CGShepherd/Shellac/docs/design_pack/AE-075G_SCH108_Output_Interface_and_PRE90_Compatibility_Reconciliation_Rev_A0.md

# AE-075G — SCH108 Output Interface and PRE90 Compatibility Reconciliation — Rev A0

**Project:** Shellac
**Status:** CLOSED — OUTPUT INTERFACE ELECTRICAL/NATIVE MIGRATION VALIDATED; MANUAL XY PLACEMENT OPEN
**Baseline:** `2d635647cd3ee6e4e1886cbfcbfffe43f3453116` (AE-075F)

## Purpose

AE-075G closes the SCH108 PCB-to-rear-panel balanced-output connector electrical/native migration, corrects the live THAT1646 output-source-impedance semantics, and executes an application-specific Topping PRE90 2 kOhm load discriminator without modifying historical AE-069 RUN06 evidence.

## Output harness

Selected hardware: Molex `5055780221` two-circuit right-angle SMT PCB header, `5055700201` housing and `5055721200` female crimp. H801 is left and H802 right. Pin 1 is HOT/+, pin 2 COLD/-, retention pads are mechanical/unconnected, and no 0VA conductor is present. Rear-panel XLR pin 1 and shell remain local CHASSIS bonds under AE-075B.

Native F8 validation proves H801 pad 1 `/OUTPUT_L_POS`, pad 2 `/OUTPUT_L_NEG`; H802 pad 1 `/OUTPUT_R_POS`, pad 2 `/OUTPUT_R_NEG`; retention pads are unconnected.

The imported/autogenerated H801/H802 XY coordinates are explicitly not routing or placement authority. Manual front-to-rear placement reconciliation remains open.

## THAT1646 source semantics

The live generator model records 25 Ohm output impedance per leg and 50 Ohm differential/balanced. This resolves `AE071-S01`.

## PRE90 application-specific load discriminator

The PRE90 2 kOhm balanced-input case is separate from the AE-069 RUN06 normal-load set.

- Worst absolute insertion loss versus 100 kOhm: **0.209239 dB**.
- Worst passband peak: **0.000409 dB**.
- DC absolute gate: **PASS**.
- Exact-topology HF small-signal evidence: **COMPLETE**.
- 3.21 Vrms local severe-input headroom minimum: **PASS**.
- Overall 2 kOhm load compatibility: **PASS**.

Loaded representative Shellac estimates are 0.626735 Vrms nominal, 5.720666 Vrms worst-default and 9.098397 Vrms worst-high-gain. Margins to the controlled 9.3 Vrms PRE90 0 dB balanced-input sensitivity figure are respectively 23.4280 dB, 4.2207 dB and 0.1904 dB.

The 2 kOhm electrical load is therefore accepted, but the highest representative high-gain state retains a commissioning/operating-level check because only about 0.19 dB margin exists to the published sensitivity figure.

## Configuration-control debt reconciliation

AE-075G closure also reconciles temporal coupling in recent historical assurance tests. Historical AE tests now assert the design facts and qualification boundaries owned by their own records rather than requiring later live routing-hold status, global product-population counts or unrelated blocker sets to remain frozen. Mutable current authority remains owned by `tests/test_current_decision_index.py`. A dedicated regression guard prevents the identified anti-patterns from being reintroduced across AE-071 through AE-075G assurance tests.

## Preserved boundaries

AE-075G does not modify historical AE-069 RUN06 evidence or normal-load definitions; close RUN06 prototype load/cable stability; close dynamic THD; select the final ferrite; authorise routing/layout/BOM/manufacturing freeze; freeze H801/H802 XY/orientation; or change the AE-075F B03 four-local-control-module authority.

The next controlled mechanical increment will address six-point direct main-PCB-to-top-cover support and deliberate manual front-to-rear placement. It must explicitly supersede the AE-075F carrier/local-control-board assumptions rather than rewrite AE-075D/E/F history.

## Evidence

- `simulation/config/ae075g_pre90_output.yaml`
- `simulation/scripts/ae075g_pre90_output.py`
- `simulation/results/ae075g_pre90_output/ae075g_pre90_output.json`
- `simulation/results/ae075g_pre90_output/ae075g_pre90_output.md`
- `tests/test_ae075g_output_interface_phase1.py`
- `tests/test_ae075g_output_interface_phase2.py`

This record is retained only if the fail-closed Phase-2B closure script completes targeted/full regression, deterministic generated-CAD rebuild, native hierarchical ERC, native PCB integrity, integrated preflight, decision/configuration audit and `git diff --check`.
