CGShepherd/Shellac/docs/design_pack/AE-040A_Post_F03_Production_Integrity_Reconciliation_Rev_A0.md

# AE-040A — Post-F03 Production Integrity Reconciliation

**Revision:** A0  
**Status:** ROUTING-HOLD RECONCILIATION

AE-036 originally imposed a repository-wide routing hold on:
- F01 — native PCB deletion risk;
- F02 — SCH101 cartridge load/bias/RF incompleteness;
- F03 — dual op-amp package/unit semantics.

All three are now closed by controlled, regression-tested increments.

## Closure evidence

### F01
AE-036A/B preserve native PCB and design-rule artifacts during normal clean builds.

### F02
AE-037 family closes the balanced cartridge interface and reconciles placement.

### F03
AE-038/039 family closes the 18-function / 10-package op-amp representation,
real KiCad A/B units, actual SOIC-8 pins, and explicit follower feedback.

## Disposition

The **AE-036 repository-wide routing hold is lifted**.

F04-F13 remain open. This does not constitute fabrication release. Analogue
routing may resume under SR-041 authority while controls, supply margin, BOM,
native-audit strength, CI, mechanical interface confirmation and release evidence
continue toward closure.
