CGShepherd/Shellac/docs/design_pack/AE-030_Generated_Production_Readiness_Audit.md

# AE-030 Generated Production Readiness Audit

Repository: `C:\Users\chris\Dropbox\000_Projects\000_Audio\Shellac`

## Executive status

- production gates: **18**
- CLOSED: **4**
- READY_FOR_NEXT_ACTIVITY: **6**
- PROTOTYPE_EVIDENCE_REQUIRED: **1**
- BLOCKED: **7**
- release blockers: **10**

## Gate matrix

| ID | Area | State | Release blocker | Evidence | Next action |
|---|---|---|---|---|---|
| ELEC-SIGNAL | Electrical signal chain | **CLOSED** | NO | AE-023 + AE-029; DR-037/038/039/040 implemented; analytical acceptance matrix established. | Do not reopen unless prototype evidence contradicts the controlled model. |
| ELEC-MEASURE | Prototype electrical acceptance | **PROTOTYPE_EVIDENCE_REQUIRED** | YES | AE-029 defines measured CMRR/noise/DC/EQ/overload/transient acceptance. | Build representative hardware and execute commissioning matrix. |
| MECH-ENCLOSURE | Audio enclosure / carrier / PCB datum | **CLOSED** | NO | SR-040 freezes METCASE M5502119 evidence and 220 x 140 mm PCB datum. | Retain frozen datum unless a production ECO is justified. |
| MECH-CONTROLS | Rotary control mechanics | **BLOCKED** | YES | Grayhill 71BDF30 is rejected for right-angle geometry; AE-026/027/028 select Lorlin PT pending exact MPN/sample evidence. | Close Lorlin exact-order-code and physical sample geometry gates, then perform control-hardware ECO. |
| MECH-TOP | Top-panel machining | **BLOCKED** | YES | Current top-cover stack still encodes Grayhill geometry and explicitly withholds machining release. | Regenerate top-cover stack from verified Lorlin PT + C&K hardware and panel thickness. |
| PCB-OUTLINE | PCB outline and mounting | **CLOSED** | NO | SR-040 frozen outline / four mounting holes / keep-outs. | Carry frozen outline into native board. |
| PCB-PLACEMENT | Critical placement | **READY_FOR_NEXT_ACTIVITY** | NO | SR-041 accepts manual clusters as routing baseline with zero mounting collisions. | Only local refinement within movement authority during routing. |
| PCB-NATIVE | Native KiCad board setup | **READY_FOR_NEXT_ACTIVITY** | YES | SR-043 audit requires populated frozen outline, mounting holes, unrouted state and four copper layers. | Confirm native board is four-layer: F.Cu/In1.Cu/In2.Cu/B.Cu before routing. |
| PCB-ROUTING | Native PCB routing | **BLOCKED** | YES | Current native-board audit intentionally expects an unrouted board before routing release. | Complete controlled manual routing, planes, return paths, then DRC/ERC/review. |
| PCB-FAB | Fabrication release | **BLOCKED** | YES | No production-routed/DRC-closed fabrication baseline exists yet. | After routing: run DRC/ERC, Gerber/drill inspection, fabrication manifest and release review. |
| BOM-CONTROLS | Control-hardware BOM | **BLOCKED** | YES | Controlled BOM still contains rejected Grayhill rotary parts. | Replace only after Lorlin PT production MPN/sample gate closes. |
| BOM-GENERAL | General BOM/procurement | **READY_FOR_NEXT_ACTIVITY** | YES | Controlled partial BOM exists; procurement_complete is false. | Run final BOM completeness, alternates, lifecycle and availability audit before production release. |
| DOC-AUTHORITY | Decision/document authority | **CLOSED** | NO | AE-024/025 reconciliation: zero vocabulary findings and zero current-authority contradictions. | Maintain authority classifications with future ECOs. |
| DOC-COMMISSION | Commissioning / maintenance baseline | **READY_FOR_NEXT_ACTIVITY** | NO | AE-029 provides first-hardware acceptance matrix; maintenance structure exists. | Populate measured results and fault-isolation guidance after prototype. |
| DOC-RELEASE | Production design pack | **BLOCKED** | YES | Pack structure exists but fabrication release, measured acceptance, final BOM and release manifest remain incomplete. | Assemble release pack after PCB/mechanical/prototype gates close. |
| REPRO-CLEANCLONE | Clean-clone reproducibility | **BLOCKED** | YES | Not yet demonstrated from an empty clone against pinned tool/dependency versions. | Perform clean-clone build and compare generated production artifacts before tag. |
| REPO-HYGIENE | Repository production cleanup | **READY_FOR_NEXT_ACTIVITY** | NO | Cleanup deliberately deferred until production standard is known. | Classify authoritative source, controlled evidence and release artifacts; archive/remove detritus after baseline freeze. |
| INFRA-EXTRACT | Foundry / Generator extraction | **READY_FOR_NEXT_ACTIVITY** | NO | Planned post-production extraction; Shellac still informs generic/project-specific boundary. | Extract Foundry and Generator only after production clean-clone baseline is proven. |

## Required design-pack path check

- All AE-030 required authority/acceptance paths are present.

## Live Grayhill references requiring ECO disposition

- `config/bom/shellac_bom.yaml`
- `config/procurement/sourcing_snapshot_2026-08-24.yaml`
- `generator/mechanical/control_hardware.py`
- `generator/mechanical/top_cover_stack.py`
- `generator/model/controls.py`
- `generator/model/production_readiness.py`

## Recommended execution order

1. Close Lorlin PT exact MPN and AE-028 mechanical sample gate.
2. Perform control-hardware ECO: BOM + mechanical model + top-cover stack + footprints/placement.
3. Confirm native KiCad board four-layer stack and plane intent.
4. Route the native PCB under SR-041 critical-net/manual-routing rules.
5. Run full DRC/ERC, return-path/plane review and fabrication-output inspection.
6. Complete general BOM/procurement/lifecycle audit.
7. Fabricate and commission representative hardware using AE-029.
8. Freeze measured acceptance limits and complete maintenance/fault-isolation data.
9. Assemble production design/release pack.
10. Clean-clone reproducibility audit.
11. Repository cleanup and tagged production release.
12. Extract Foundry and Generator into independent versioned dependencies.

## Interpretation

The project is no longer primarily blocked by signal-chain design.
The critical path is now controls/mechanics -> native routing/fabrication -> prototype evidence -> release/reproducibility.
