CGShepherd/Shellac/docs/procurement/AE028_PT_Mechanical_Sample_Basket.md

# AE-028 PT mechanical sample basket

Preferred sources: established UK distributors.

Indicative basket:
- 1 × Lorlin PT6534 or equivalent PT 2P5T mechanical proxy
- 1 × Lorlin PT6528 spacer kit
- 1 × Lorlin PT602-003 or PT602-011 additional wafer

Important:
These are for mechanical validation only. Do not substitute them into the
production BOM for the required gold-contact switches.
