CGShepherd/Shellac/docs/design_pack/AE-025_Current_Authority_and_Design_Pack_Reconciliation_Rev_A0.md

# AE-025 — Current Authority and Design-Pack Reconciliation

**Revision:** A0
**Base:** `develop` at `47a5fcabfef4239fcfe78bf97901dce75b4e7301`

AE-024 reported 26 apparent status contradictions. Most are valid historical-state
evidence rather than current defects. AE-025 therefore reconciles only present-tense
authority surfaces.

Changes:
- separates narrative lifecycle statuses from authoritative current statuses;
- adds explicit current-authority vs historical-evidence classification;
- updates README from stale SR-034/G3-023 baseline language;
- updates design-pack index for implemented DR-038/039 and AE-023;
- updates maintenance skeleton for implemented service links/DC block;
- teaches AE-024 to report contradictions only on current-authority surfaces.

Historical AE-016/017/019/020 records remain unchanged.

Expected result after rerunning AE-024:
- zero status-vocabulary findings;
- zero unexpected current-authority contradictions;
- numerous baseline keyword hits may remain because historical analyses correctly
  record the baseline they examined.
