CGShepherd/Shellac/docs/AE-022_DR038_Full_SCH101_Precision_Migration_Rev_A0.md

# AE-022 — DR-038 Full SCH101 Precision Migration

Large subsystem migration: 4x LT5400-7 differential converter, low-impedance
precision gain legs, service-link configuration, native KiCad symbol/footprint,
placement ownership, BOM and decision-register migration. Once this reaches
green pytest plus normal build/ERC, proceed to full schematic human review/ERC
and then PCB layout.
