CGShepherd/Shellac/docs/AE-022F_LT5400_Symbol_Contract_Closure_Rev_A0.md

# AE-022F — LT5400 Symbol-Contract Closure

AE-022E showed that the remaining defect lies at the LT5400 primitive boundary.

AE-022F gives the LT5400 a deliberately spacious logical schematic symbol while
preserving the physical MS8E footprint and pin numbering. Pins 1–4 are separated
on the left, pins 5–8 on the right, and EP9 is isolated below the body.

SCH101 returns to explicit conductive geometry because the internal electrical
audit does not electrically join identical labels at separate coordinates.

Primitive-level tests now verify nine unique semantic pin locations before the
SCH101 builder is exercised.
