CGShepherd/Shellac/docs/AE-017_Generated_Atomic_Migration_Dependency_Map.md

# AE-017 Generated DR-038 / DR-039 Dependency Map

Repository scanned: `C:\Users\chris\Dropbox\000_Projects\000_Audio\Shellac`

## Summary

- matched files: **80**
- matched references: **505**

This report is evidence for an atomic migration. A file appearing here is
not automatically changed; it is a review surface that must be dispositioned.

## SCH101_NUMERIC

| File | Contract class | References |
|---|---|---:|
| `docs/AE-010_SCH101_Gain_Selector_Closure_Rev_A.md` | controlled documentation | 2 |
| `docs/AE-011_End_to_End_Signal_Chain_Closure_Rev_A0.md` | controlled documentation | 1 |
| `docs/AE-013_SCH101_Noise_CMRR_Review_Rev_A0.md` | controlled documentation | 1 |
| `docs/AE-014_SCH101_Precision_Architecture_Downselect_Rev_A0.md` | controlled documentation | 7 |
| `docs/AE-016A_AE016_Regression_Repair_Rev_A0.md` | controlled documentation | 1 |
| `docs/AE-017_Atomic_Migration_Dependency_Mapping_Gate_Rev_A0.md` | controlled documentation | 4 |
| `docs/decisions/DR-038_SCH101_Precision_Architecture_SELECTED.md` | controlled documentation | 1 |
| `generator/blocks/balanced_input.py` | CAD builder | 12 |
| `generator/core/components.py` | CAD infrastructure | 1 |
| `generator/model/balanced_input.py` | electrical/analysis model | 13 |
| `generator/model/sch101_precision_analysis.py` | electrical/analysis model | 4 |
| `generator/model/sch101_precision_candidate.py` | electrical/analysis model | 1 |
| `out/kicad/ProjectShellac_SCH101.kicad_sch` | repository/support | 18 |
| `out/kicad/ProjectShellac_SCH103.kicad_sch` | repository/support | 1 |
| `out/layout/footprint_contract.json` | repository/support | 14 |
| `out/layout/kicad_native_pipeline.json` | repository/support | 14 |
| `out/pcb/ProjectShellac_Gate3A_Review.kicad_pcb` | repository/support | 14 |
| `scripts/report_balanced_input_gain.py` | repository/support | 4 |
| `tests/test_ae017_dependency_map.py` | regression contract | 5 |
| `tests/test_balanced_input.py` | regression contract | 5 |
| `tests/test_balanced_input_gain.py` | regression contract | 3 |
| `tests/test_dr038_dr039.py` | regression contract | 3 |
| `tools/ae017_dependency_map.py` | repository/support | 12 |

## SCH101_CAD

| File | Contract class | References |
|---|---|---:|
| `docs/AE-017_Atomic_Migration_Dependency_Mapping_Gate_Rev_A0.md` | controlled documentation | 4 |
| `docs/SR-006_SCH101_DIP_Switch_Closure_Rev_A.md` | controlled documentation | 1 |
| `generator/blocks/balanced_input.py` | CAD builder | 5 |
| `generator/core/components.py` | CAD infrastructure | 1 |
| `generator/core/pins.py` | CAD infrastructure | 1 |
| `generator/layout/placement_clusters.py` | layout | 4 |
| `generator/writers/kicad9.py` | repository/support | 4 |
| `out/kicad/ProjectShellac.kicad_sym` | repository/support | 2 |
| `out/kicad/ProjectShellac_SCH101.kicad_sch` | repository/support | 20 |
| `out/kicad/ProjectShellac_SCH103.kicad_sch` | repository/support | 2 |
| `out/kicad/ProjectShellac_SCH104.kicad_sch` | repository/support | 2 |
| `out/kicad/ProjectShellac_SCH105.kicad_sch` | repository/support | 2 |
| `out/kicad/ProjectShellac_SCH106.kicad_sch` | repository/support | 2 |
| `out/kicad/ProjectShellac_SCH107.kicad_sch` | repository/support | 2 |
| `out/kicad/ProjectShellac_SCH108.kicad_sch` | repository/support | 2 |
| `out/kicad/ProjectShellac_SCH109.kicad_sch` | repository/support | 2 |
| `out/layout/cluster_placement_baseline.json` | repository/support | 4 |
| `out/layout/detailed_placement_readiness.json` | repository/support | 8 |
| `out/layout/footprint_contract.json` | repository/support | 10 |
| `out/layout/kicad_native_pipeline.json` | repository/support | 5 |
| `out/layout/preliminary_placement_baseline.json` | repository/support | 4 |
| `out/pcb/ProjectShellac_Gate3A_Review.kicad_pcb` | repository/support | 5 |
| `tests/test_ae017_dependency_map.py` | regression contract | 4 |
| `tests/test_balanced_input.py` | regression contract | 7 |
| `tests/test_kicad_writer_instances.py` | regression contract | 2 |
| `tests/test_pin_connectivity.py` | regression contract | 1 |
| `tests/test_root_hierarchy.py` | regression contract | 1 |
| `tools/ae017_dependency_map.py` | repository/support | 8 |

## SCH103_OUTPUT

| File | Contract class | References |
|---|---|---:|
| `APPLY_DR039_PATCH.py` | repository/support | 8 |
| `RESTORE_SCH103_BASELINE.py` | repository/support | 8 |
| `docs/AE-015_Full_Chain_Noise_DC_Review_Rev_A0.md` | controlled documentation | 2 |
| `docs/SR-004_SCH107_Pin_Aware_Conversion_Rev_A.md` | controlled documentation | 1 |
| `docs/SR-021_SCH107_Human_Reviewable_Conversion_Rev_A.md` | controlled documentation | 1 |
| `docs/SR-024_SCH103_Human_Reviewable_Rev_A.md` | controlled documentation | 1 |
| `docs/updates/AE016B_UPDATE_MANIFEST.md` | controlled documentation | 1 |
| `docs/updates/AE016_UPDATE_MANIFEST.md` | controlled documentation | 1 |
| `generator/blocks/replay_eq.py` | CAD builder | 6 |
| `generator/blocks/rumble_filter.py` | CAD builder | 2 |
| `generator/commissioning/model.py` | repository/support | 4 |
| `generator/model/shellac.py` | electrical/analysis model | 6 |
| `manifest.json` | repository/support | 1 |
| `out/commissioning/commissioning_baseline.json` | repository/support | 4 |
| `out/kicad/ProjectShellac.kicad_sch` | repository/support | 8 |
| `out/kicad/ProjectShellac_SCH103.kicad_sch` | repository/support | 8 |
| `out/kicad/ProjectShellac_SCH107.kicad_sch` | repository/support | 2 |
| `out/layout/footprint_contract.json` | repository/support | 6 |
| `out/layout/kicad_native_pipeline.json` | repository/support | 6 |
| `out/pcb/ProjectShellac_Gate3A_Review.kicad_pcb` | repository/support | 6 |
| `tests/test_pin_connectivity.py` | regression contract | 2 |
| `tests/test_sch103_human_readable.py` | regression contract | 1 |
| `tests/test_sch107_human_readable.py` | regression contract | 1 |
| `tools/ae017_dependency_map.py` | repository/support | 5 |

## DR039

| File | Contract class | References |
|---|---|---:|
| `APPLY_DR039_PATCH.py` | repository/support | 8 |
| `APPLY_SIGNAL_CHAIN_PATCH.py` | repository/support | 3 |
| `REPAIR_SIGNAL_CHAIN.py` | repository/support | 1 |
| `RESTORE_SCH103_BASELINE.py` | repository/support | 5 |
| `docs/AE-015_Full_Chain_Noise_DC_Review_Rev_A0.md` | controlled documentation | 7 |
| `docs/AE-016A_AE016_Regression_Repair_Rev_A0.md` | controlled documentation | 2 |
| `docs/AE-016B_Full_Regression_Staging_Repair_Rev_A0.md` | controlled documentation | 2 |
| `docs/AE-016_DR038_DR039_Implementation_Baseline_Rev_A0.md` | controlled documentation | 4 |
| `docs/AE-017_Atomic_Migration_Dependency_Mapping_Gate_Rev_A0.md` | controlled documentation | 3 |
| `docs/decisions/DR-039_Common_Post_EQ_DC_Block_PROPOSED.md` | controlled documentation | 3 |
| `docs/decisions/DR-039_Common_Post_EQ_DC_Block_SELECTED.md` | controlled documentation | 4 |
| `docs/updates/AE015_UPDATE_MANIFEST.md` | controlled documentation | 1 |
| `docs/updates/AE016A_UPDATE_MANIFEST.md` | controlled documentation | 2 |
| `docs/updates/AE016B_UPDATE_MANIFEST.md` | controlled documentation | 2 |
| `docs/updates/AE016_UPDATE_MANIFEST.md` | controlled documentation | 3 |
| `docs/updates/AE017_UPDATE_MANIFEST.md` | controlled documentation | 1 |
| `generator/blocks/power_entry.py` | CAD builder | 4 |
| `generator/model/post_eq_dc_block.py` | electrical/analysis model | 2 |
| `generator/model/signal_chain_noise_dc.py` | electrical/analysis model | 2 |
| `out/kicad/ProjectShellac_SCH106.kicad_sch` | repository/support | 2 |
| `out/layout/footprint_contract.json` | repository/support | 2 |
| `out/layout/kicad_native_pipeline.json` | repository/support | 2 |
| `out/pcb/ProjectShellac_Gate3A_Review.kicad_pcb` | repository/support | 2 |
| `tests/test_ae017_dependency_map.py` | regression contract | 1 |
| `tests/test_dr038_dr039.py` | regression contract | 2 |
| `tests/test_signal_chain_noise_dc.py` | regression contract | 1 |
| `tools/ae017_dependency_map.py` | repository/support | 10 |

## ANALYSIS

| File | Contract class | References |
|---|---|---:|
| `APPLY_SIGNAL_CHAIN_PATCH.py` | repository/support | 2 |
| `REPAIR_SIGNAL_CHAIN.py` | repository/support | 2 |
| `docs/AE-012_All_State_Gain_Headroom_Closure_Rev_A0.md` | controlled documentation | 2 |
| `docs/AE-013_SCH101_Noise_CMRR_Review_Rev_A0.md` | controlled documentation | 5 |
| `docs/AE-014_SCH101_Precision_Architecture_Downselect_Rev_A0.md` | controlled documentation | 10 |
| `docs/AE-015_Full_Chain_Noise_DC_Review_Rev_A0.md` | controlled documentation | 4 |
| `docs/AE-016A_AE016_Regression_Repair_Rev_A0.md` | controlled documentation | 2 |
| `docs/decisions/DR-038_SCH101_Precision_Architecture_PROPOSED.md` | controlled documentation | 4 |
| `docs/decisions/DR-038_SCH101_Precision_Architecture_SELECTED.md` | controlled documentation | 1 |
| `docs/decisions/DR-039_Common_Post_EQ_DC_Block_PROPOSED.md` | controlled documentation | 1 |
| `docs/updates/AE012_UPDATE_MANIFEST.md` | controlled documentation | 4 |
| `docs/updates/AE013_UPDATE_MANIFEST.md` | controlled documentation | 4 |
| `docs/updates/AE014_UPDATE_MANIFEST.md` | controlled documentation | 4 |
| `docs/updates/AE015_UPDATE_MANIFEST.md` | controlled documentation | 4 |
| `docs/updates/AE016A_UPDATE_MANIFEST.md` | controlled documentation | 2 |
| `docs/updates/AE016B_UPDATE_MANIFEST.md` | controlled documentation | 1 |
| `docs/updates/AE016_UPDATE_MANIFEST.md` | controlled documentation | 1 |
| `docs/updates/DR037_UPDATE_MANIFEST.md` | controlled documentation | 2 |
| `generator/model/sch101_precision_analysis.py` | electrical/analysis model | 1 |
| `generator/model/sch101_precision_candidate.py` | electrical/analysis model | 1 |
| `generator/model/signal_chain_analysis.py` | electrical/analysis model | 1 |
| `generator/model/signal_chain_noise_dc.py` | electrical/analysis model | 2 |
| `tests/test_dr038_dr039.py` | regression contract | 1 |
| `tests/test_sch101_precision_analysis.py` | regression contract | 1 |
| `tests/test_sch101_precision_candidate.py` | regression contract | 1 |
| `tests/test_signal_chain_analysis.py` | regression contract | 1 |
| `tests/test_signal_chain_noise_dc.py` | regression contract | 1 |
| `tools/ae017_dependency_map.py` | repository/support | 12 |

## Atomic migration gates

### DR-038 / SCH101

The migration is not complete until all of these move together:

1. electrical constants and gain settings;
2. physical LT5400-7 component/symbol/footprint representation;
3. removal/replacement of the ordinary DIP gain selector;
4. precision service-link implementation;
5. SCH101 builder values and annotations;
6. component/BOM/procurement records;
7. numeric gain regressions;
8. rendered-CAD/refdes regressions;
9. AE-012 headroom regression;
10. AE-013/014 noise/CMRR regression.

### DR-039 / SCH103

The migration is not complete until all of these move together:

1. post-EQ DC-block electrical model;
2. SCH103 output builder and test-point allocation;
3. physical film-capacitor selection/footprint;
4. PCB placement allowance;
5. component-count/refdes contracts;
6. replay-curve regression including the ~0.48 Hz pole;
7. AE-012 headroom update;
8. AE-015 DC/noise update;
9. rumble bypass/filter switching transient tests;
10. power-up/power-down transient acceptance.

## Detailed hits

| Category | Token | File | Line | Context |
|---|---|---|---:|---|
| SCH103_OUTPUT | `replay_eq.py` | `APPLY_DR039_PATCH.py` | 2 | path=Path("generator/blocks/replay_eq.py") |
| DR039 | `DR-039` | `APPLY_DR039_PATCH.py` | 4 | if "DR-039 common post-EQ DC block" in text: |
| DR039 | `DR-039` | `APPLY_DR039_PATCH.py` | 5 | print("replay_eq.py already contains DR-039; no change.") |
| SCH103_OUTPUT | `replay_eq.py` | `APPLY_DR039_PATCH.py` | 5 | print("replay_eq.py already contains DR-039; no change.") |
| SCH103_OUTPUT | `output_end = Point(420` | `APPLY_DR039_PATCH.py` | 7 | old = ''' output_end = Point(420, u2_out.y) |
| SCH103_OUTPUT | `TP{base}4` | `APPLY_DR039_PATCH.py` | 9 | f"TP{base}4", f"{channel}_EQ_OUT", Point(395, u2_out.y + 5.08) |
| SCH103_OUTPUT | `_EQ_OUT` | `APPLY_DR039_PATCH.py` | 9 | f"TP{base}4", f"{channel}_EQ_OUT", Point(395, u2_out.y + 5.08) |
| DR039 | `DR-039` | `APPLY_DR039_PATCH.py` | 15 | new = ''' # DR-039 common post-EQ DC block before the SCH107 filter/bypass split. |
| SCH103_OUTPUT | `TP{base}4` | `APPLY_DR039_PATCH.py` | 17 | f"TP{base}4", f"{channel}_EQ_RAW", Point(395, u2_out.y + 5.08) |
| DR039 | `1u` | `APPLY_DR039_PATCH.py` | 20 | f"C{base}60", "1u", Point(425, u2_out.y), |
| DR039 | `DR-039` | `APPLY_DR039_PATCH.py` | 22 | function="DR-039 common post-EQ DC block", |
| DR039 | `330k` | `APPLY_DR039_PATCH.py` | 27 | f"R{base}60", "330k", Point(455, u2_out.y + 15), |
| DR039 | `DR-039` | `APPLY_DR039_PATCH.py` | 28 | tolerance="1%", function="DR-039 downstream DC reference" |
| SCH103_OUTPUT | `_EQ_OUT` | `APPLY_DR039_PATCH.py` | 31 | f"TP{base}5", f"{channel}_EQ_OUT", Point(455, u2_out.y + 5.08) |
| DR039 | `DR-039` | `APPLY_DR039_PATCH.py` | 43 | print("Patched replay_eq.py for DR-039") |
| SCH103_OUTPUT | `replay_eq.py` | `APPLY_DR039_PATCH.py` | 43 | print("Patched replay_eq.py for DR-039") |
| ANALYSIS | `signal_chain_analysis` | `APPLY_SIGNAL_CHAIN_PATCH.py` | 2 | p=Path("generator/model/signal_chain_analysis.py") |
| DR039 | `post_eq_dc_block` | `APPLY_SIGNAL_CHAIN_PATCH.py` | 4 | if "post_eq_dc_block" not in t: |
| DR039 | `post_eq_dc_block` | `APPLY_SIGNAL_CHAIN_PATCH.py` | 7 | "from .output_driver import DIFFERENTIAL_GAIN_LINEAR, DESIGN_OUTPUT_RMS_V\nfrom .post_eq_dc_block import magnitude as post_eq_dc_magnitude" |
| ANALYSIS | `signal_chain_analysis` | `APPLY_SIGNAL_CHAIN_PATCH.py` | 14 | print("Patched signal_chain_analysis.py for DR-039") |
| DR039 | `DR-039` | `APPLY_SIGNAL_CHAIN_PATCH.py` | 14 | print("Patched signal_chain_analysis.py for DR-039") |
| ANALYSIS | `signal_chain_analysis` | `REPAIR_SIGNAL_CHAIN.py` | 2 | p = Path("generator/model/signal_chain_analysis.py") |
| DR039 | `post_eq_dc_block` | `REPAIR_SIGNAL_CHAIN.py` | 4 | t = t.replace("\nfrom .post_eq_dc_block import magnitude as post_eq_dc_magnitude", "") |
| ANALYSIS | `AE-012` | `REPAIR_SIGNAL_CHAIN.py` | 10 | print("AE-012 signal-chain model is at its pre-DR039 controlled baseline.") |
| SCH103_OUTPUT | `replay_eq.py` | `RESTORE_SCH103_BASELINE.py` | 3 | path = Path("generator/blocks/replay_eq.py") |
| DR039 | `DR-039` | `RESTORE_SCH103_BASELINE.py` | 6 | dr039 = ''' # DR-039 common post-EQ DC block before the SCH107 filter/bypass split. |
| SCH103_OUTPUT | `TP{base}4` | `RESTORE_SCH103_BASELINE.py` | 8 | f"TP{base}4", f"{channel}_EQ_RAW", Point(395, u2_out.y + 5.08) |
| DR039 | `1u` | `RESTORE_SCH103_BASELINE.py` | 11 | f"C{base}60", "1u", Point(425, u2_out.y), |
| DR039 | `DR-039` | `RESTORE_SCH103_BASELINE.py` | 13 | function="DR-039 common post-EQ DC block", |
| DR039 | `330k` | `RESTORE_SCH103_BASELINE.py` | 18 | f"R{base}60", "330k", Point(455, u2_out.y + 15), |
| DR039 | `DR-039` | `RESTORE_SCH103_BASELINE.py` | 19 | tolerance="1%", function="DR-039 downstream DC reference" |
| SCH103_OUTPUT | `_EQ_OUT` | `RESTORE_SCH103_BASELINE.py` | 22 | f"TP{base}5", f"{channel}_EQ_OUT", Point(455, u2_out.y + 5.08) |
| SCH103_OUTPUT | `output_end = Point(420` | `RESTORE_SCH103_BASELINE.py` | 32 | baseline = ''' output_end = Point(420, u2_out.y) |
| SCH103_OUTPUT | `TP{base}4` | `RESTORE_SCH103_BASELINE.py` | 34 | f"TP{base}4", f"{channel}_EQ_OUT", Point(395, u2_out.y + 5.08) |
| SCH103_OUTPUT | `_EQ_OUT` | `RESTORE_SCH103_BASELINE.py` | 34 | f"TP{base}4", f"{channel}_EQ_OUT", Point(395, u2_out.y + 5.08) |
| SCH103_OUTPUT | `replay_eq.py` | `RESTORE_SCH103_BASELINE.py` | 44 | print("Restored replay_eq.py to pre-DR039 physical generator baseline.") |
| SCH103_OUTPUT | `replay_eq.py` | `RESTORE_SCH103_BASELINE.py` | 46 | print("replay_eq.py already at pre-DR039 physical baseline.") |
| SCH101_NUMERIC | `3.48` | `docs/AE-010_SCH101_Gain_Selector_Closure_Rev_A.md` | 10 | followed by a fixed 3.48× differential converter. That implied 13.92× total |
| SCH101_NUMERIC | `3.48` | `docs/AE-010_SCH101_Gain_Selector_Closure_Rev_A.md` | 23 | 3. fixed 3.48× precision differential converter; |
| SCH101_NUMERIC | `3.48` | `docs/AE-011_End_to_End_Signal_Chain_Closure_Rev_A0.md` | 37 | - fixed 3.48x differential conversion; |
| ANALYSIS | `AE-012` | `docs/AE-012_All_State_Gain_Headroom_Closure_Rev_A0.md` | 1 | # AE-012 — Project Shellac All-State Gain and Headroom Closure |
| ANALYSIS | `AE-012` | `docs/AE-012_All_State_Gain_Headroom_Closure_Rev_A0.md` | 11 | AE-012 performs a dense end-to-end gain/headroom sweep of: |
| ANALYSIS | `AE-013` | `docs/AE-013_SCH101_Noise_CMRR_Review_Rev_A0.md` | 1 | # AE-013 — SCH101 Noise and CMRR Design-Assurance Review |
| ANALYSIS | `AE-012` | `docs/AE-013_SCH101_Noise_CMRR_Review_Rev_A0.md` | 10 | AE-012 closed the end-to-end gain/headroom envelope. The next assurance step was integrated noise and common-mode rejection. |
| SCH101_NUMERIC | `3.48` | `docs/AE-013_SCH101_Noise_CMRR_Review_Rev_A0.md` | 92 | - differential converter: 10 kΩ / 34.8 kΩ -> approximately 1 kΩ / 3.48 kΩ. |
| ANALYSIS | `AE-013` | `docs/AE-013_SCH101_Noise_CMRR_Review_Rev_A0.md` | 109 | A matched thin-film resistor network or networks are likely preferable to eight independent precision resistors, but component down-selection is deliberately no |
| ANALYSIS | `AE-013` | `docs/AE-013_SCH101_Noise_CMRR_Review_Rev_A0.md` | 113 | AE-013 does **not** alter SCH101 component values or footprints. |
| ANALYSIS | `AE-012` | `docs/AE-013_SCH101_Noise_CMRR_Review_Rev_A0.md` | 119 | - AE-012 gain/headroom: remains GREEN. |
| ANALYSIS | `AE-014` | `docs/AE-014_SCH101_Precision_Architecture_Downselect_Rev_A0.md` | 1 | # AE-014 — SCH101 Precision Architecture Down-Selection |
| ANALYSIS | `AE-013` | `docs/AE-014_SCH101_Precision_Architecture_Downselect_Rev_A0.md` | 10 | AE-013 identified two coupled weaknesses in the controlled SCH101 implementation: resistor-network Johnson noise and tolerance-limited CMRR. |
| ANALYSIS | `AE-014` | `docs/AE-014_SCH101_Precision_Architecture_Downselect_Rev_A0.md` | 12 | AE-014 recommends solving both without changing the fundamental balanced-input topology or the established 14/18/22 dB user gain choices. |
| SCH101_NUMERIC | `3.48` | `docs/AE-014_SCH101_Precision_Architecture_Downselect_Rev_A0.md` | 18 | 3. change the differential converter from the non-standard 3.48 ratio to a precision **4.000 ratio**; |
| SCH101_NUMERIC | `3.48` | `docs/AE-014_SCH101_Precision_Architecture_Downselect_Rev_A0.md` | 26 | ## 1. Why 4.00x rather than retaining 3.48x |
| SCH101_NUMERIC | `3.48` | `docs/AE-014_SCH101_Precision_Architecture_Downselect_Rev_A0.md` | 28 | The controlled 3.48x converter uses 10 kΩ / 34.8 kΩ. It is electrically valid but awkward as a high-precision monolithic ratio. |
| ANALYSIS | `AE-014` | `docs/AE-014_SCH101_Precision_Architecture_Downselect_Rev_A0.md` | 86 | **B — practical prototype solution:** individually selected 0.01% thin-film resistors for the 249 Ω / 750 Ω / 1.91 kΩ segments, placed as geometrically and ther |
| SCH101_NUMERIC | `3.48` | `docs/AE-014_SCH101_Precision_Architecture_Downselect_Rev_A0.md` | 90 | ## 5. Alternative considered: preserve 3.48x |
| SCH101_NUMERIC | `3.48` | `docs/AE-014_SCH101_Precision_Architecture_Downselect_Rev_A0.md` | 92 | Retaining 3.48x would minimise mathematical change, but it forces either: |
| SCH101_NUMERIC | `3.48` | `docs/AE-014_SCH101_Precision_Architecture_Downselect_Rev_A0.md` | 100 | **Recommendation: reject the 3.48x converter for the next SCH101 revision.** |
| ANALYSIS | `AE-013` | `docs/AE-014_SCH101_Precision_Architecture_Downselect_Rev_A0.md` | 104 | AE-013 estimated the current DEFAULT front end at roughly 18 nV/√Hz input-referred. |
| ANALYSIS | `AE-014` | `docs/AE-014_SCH101_Precision_Architecture_Downselect_Rev_A0.md` | 106 | The AE-014 candidate is below 9.5 nV/√Hz in the same first-order model. The improvement is approximately 6 dB and comes mainly from lowering the feedback/differ |
| ANALYSIS | `AE-013` | `docs/AE-014_SCH101_Precision_Architecture_Downselect_Rev_A0.md` | 138 | AE-013 found no controlled system CMRR requirement. AE-014 therefore proposes requirements for formal adoption: |
| ANALYSIS | `AE-014` | `docs/AE-014_SCH101_Precision_Architecture_Downselect_Rev_A0.md` | 138 | AE-013 found no controlled system CMRR requirement. AE-014 therefore proposes requirements for formal adoption: |
| SCH101_NUMERIC | `3.48` | `docs/AE-014_SCH101_Precision_Architecture_Downselect_Rev_A0.md` | 153 | - replace 3.48x converter with 4.00x precision converter; |
| ANALYSIS | `AE-012` | `docs/AE-014_SCH101_Precision_Architecture_Downselect_Rev_A0.md` | 170 | 5. rerun AE-012 headroom regression; |
| ANALYSIS | `AE-013` | `docs/AE-014_SCH101_Precision_Architecture_Downselect_Rev_A0.md` | 171 | 6. rerun AE-013/014 noise regression; |
| ANALYSIS | `AE-015` | `docs/AE-015_Full_Chain_Noise_DC_Review_Rev_A0.md` | 1 | # AE-015 — Full-Chain Noise and DC-Offset Review |
| ANALYSIS | `AE-015` | `docs/AE-015_Full_Chain_Noise_DC_Review_Rev_A0.md` | 11 | AE-015 extends the end-to-end review beyond gain/headroom into: |
| SCH103_OUTPUT | `POST_EQ` | `docs/AE-015_Full_Chain_Noise_DC_Review_Rev_A0.md` | 77 | The non-flat SCH103 path can then produce approximately **1.7 V DC at POST_EQ**, and the direct-coupled complete chain can exceed **3 V differential DC at the X |
| DR039 | `1.0 µF` | `docs/AE-015_Full_Chain_Noise_DC_Review_Rev_A0.md` | 100 | - series capacitor: **1.0 µF film**; |
| DR039 | `0.48 Hz` | `docs/AE-015_Full_Chain_Noise_DC_Review_Rev_A0.md` | 102 | - first-order corner: approximately **0.48 Hz**. |
| DR039 | `0.48 Hz` | `docs/AE-015_Full_Chain_Noise_DC_Review_Rev_A0.md` | 130 | The proposed 0.48 Hz high-pass pole is more than an order of magnitude below the existing 15 Hz rumble filter and about two orders below the 50 Hz RIAA low-freq |
| ANALYSIS | `AE-012` | `docs/AE-015_Full_Chain_Noise_DC_Review_Rev_A0.md` | 137 | - AE-012 headroom; |
| ANALYSIS | `AE-015` | `docs/AE-015_Full_Chain_Noise_DC_Review_Rev_A0.md` | 138 | - AE-015 noise; |
| DR039 | `DR-039` | `docs/AE-015_Full_Chain_Noise_DC_Review_Rev_A0.md` | 146 | Therefore DR-039 must be implemented together with: |
| SCH103_OUTPUT | `POST_EQ` | `docs/AE-015_Full_Chain_Noise_DC_Review_Rev_A0.md` | 166 | - direct-coupled POST_EQ -> rumble-bypass -> output DC path. |
| DR039 | `DR-039` | `docs/AE-015_Full_Chain_Noise_DC_Review_Rev_A0.md` | 170 | **DR-039 — Common post-EQ DC block** |
| DR039 | `1.0 µF` | `docs/AE-015_Full_Chain_Noise_DC_Review_Rev_A0.md` | 172 | Add a 1.0 µF film / 330 kΩ first-order DC block per channel immediately after SCH103 and before the SCH107 bypass split. |
| DR039 | `DR-039` | `docs/AE-015_Full_Chain_Noise_DC_Review_Rev_A0.md` | 178 | 1. implement DR-039 in the controlled model and SCH103/SCH107 interface; |
| SCH101_NUMERIC | `3.48` | `docs/AE-016A_AE016_Regression_Repair_Rev_A0.md` | 6 | The existing suite explicitly freezes the active converter at 3.48x. That test |
| DR039 | `DR-039` | `docs/AE-016A_AE016_Regression_Repair_Rev_A0.md` | 13 | - retains DR-039 as the implementable independent change; |
| ANALYSIS | `signal_chain_analysis` | `docs/AE-016A_AE016_Regression_Repair_Rev_A0.md` | 14 | - removes the AE016 patch to `signal_chain_analysis.py` from the apply process; |
| DR039 | `DR-039` | `docs/AE-016A_AE016_Regression_Repair_Rev_A0.md` | 15 | - makes the SCH103 DR-039 patch idempotent. |
| ANALYSIS | `sch101_precision_candidate` | `docs/AE-016A_AE016_Regression_Repair_Rev_A0.md` | 19 | `sch101_precision_candidate.py` for the next controlled migration. |
| DR039 | `DR-039` | `docs/AE-016B_Full_Regression_Staging_Repair_Rev_A0.md` | 4 | SCH101 model and DR-039 in the SCH103 physical builder. AE-016A repaired the |
| DR039 | `DR-039` | `docs/AE-016B_Full_Regression_Staging_Repair_Rev_A0.md` | 8 | DR-039 analytical model and selected decision. Both DR-038 and DR-039 will be |
| DR039 | `DR-039` | `docs/AE-016_DR038_DR039_Implementation_Baseline_Rev_A0.md` | 1 | # AE-016 — DR-038 / DR-039 Implementation Baseline |
| DR039 | `DR-039` | `docs/AE-016_DR038_DR039_Implementation_Baseline_Rev_A0.md` | 5 | This update converts DR-038 and DR-039 into the controlled electrical baseline. |
| DR039 | `DR-039` | `docs/AE-016_DR038_DR039_Implementation_Baseline_Rev_A0.md` | 10 | DR-039 inserts a 1 µF film / 330 kΩ common post-EQ DC block before the SCH107 |
| DR039 | `0.48 Hz` | `docs/AE-016_DR038_DR039_Implementation_Baseline_Rev_A0.md` | 11 | filter/bypass split. Its nominal corner is ~0.48 Hz and its calculated loss at |
| DR039 | `DR-039` | `docs/AE-017_Atomic_Migration_Dependency_Mapping_Gate_Rev_A0.md` | 10 | AE-016 demonstrated that DR-038 and DR-039 cannot safely be inserted by changing |
| SCH101_NUMERIC | `3.48` | `docs/AE-017_Atomic_Migration_Dependency_Mapping_Gate_Rev_A0.md` | 22 | 1. numerical — the active test suite explicitly requires a 3.48x differential |
| SCH101_CAD | `R112` | `docs/AE-017_Atomic_Migration_Dependency_Mapping_Gate_Rev_A0.md` | 24 | 2. rendered CAD — tests explicitly require `SW1011`, `R112`, `R113`, `R114` |
| SCH101_CAD | `R113` | `docs/AE-017_Atomic_Migration_Dependency_Mapping_Gate_Rev_A0.md` | 24 | 2. rendered CAD — tests explicitly require `SW1011`, `R112`, `R113`, `R114` |
| SCH101_CAD | `R114` | `docs/AE-017_Atomic_Migration_Dependency_Mapping_Gate_Rev_A0.md` | 24 | 2. rendered CAD — tests explicitly require `SW1011`, `R112`, `R113`, `R114` |
| SCH101_CAD | `SW1011` | `docs/AE-017_Atomic_Migration_Dependency_Mapping_Gate_Rev_A0.md` | 24 | 2. rendered CAD — tests explicitly require `SW1011`, `R112`, `R113`, `R114` |
| SCH101_NUMERIC | `21680` | `docs/AE-017_Atomic_Migration_Dependency_Mapping_Gate_Rev_A0.md` | 25 | and the current 4420 / 8280 / 21680 resistor segmentation. |
| SCH101_NUMERIC | `4420` | `docs/AE-017_Atomic_Migration_Dependency_Mapping_Gate_Rev_A0.md` | 25 | and the current 4420 / 8280 / 21680 resistor segmentation. |
| SCH101_NUMERIC | `8280` | `docs/AE-017_Atomic_Migration_Dependency_Mapping_Gate_Rev_A0.md` | 25 | and the current 4420 / 8280 / 21680 resistor segmentation. |
| DR039 | `DR-039` | `docs/AE-017_Atomic_Migration_Dependency_Mapping_Gate_Rev_A0.md` | 27 | SCH103 has a separately frozen replay-EQ transfer-function topology. DR-039 must |
| DR039 | `DR-039` | `docs/AE-017_Atomic_Migration_Dependency_Mapping_Gate_Rev_A0.md` | 49 | Do not implement DR-038/DR-039 until the generated map has been reviewed and |
| SCH103_OUTPUT | `POST_EQ` | `docs/SR-004_SCH107_Pin_Aware_Conversion_Rev_A.md` | 16 | - POST_EQ input net; |
| SCH101_CAD | `DIP_Switch_Block` | `docs/SR-006_SCH101_DIP_Switch_Closure_Rev_A.md` | 8 | was the missing embedded definition for `ProjectShellac:DIP_Switch_Block`. |
| SCH103_OUTPUT | `POST_EQ` | `docs/SR-021_SCH107_Human_Reviewable_Conversion_Rev_A.md` | 28 | POST_EQ -> input TP -> HP section A -> stage TP -> HP section B |
| SCH103_OUTPUT | `POST_EQ` | `docs/SR-024_SCH103_Human_Reviewable_Rev_A.md` | 5 | treble selector and 2.1x recovery stage to POST_EQ. |
| ANALYSIS | `AE-013` | `docs/decisions/DR-038_SCH101_Precision_Architecture_PROPOSED.md` | 5 | **Evidence:** AE-013, AE-014 |
| ANALYSIS | `AE-014` | `docs/decisions/DR-038_SCH101_Precision_Architecture_PROPOSED.md` | 5 | **Evidence:** AE-013, AE-014 |
| ANALYSIS | `AE-013` | `docs/decisions/DR-038_SCH101_Precision_Architecture_PROPOSED.md` | 25 | - removes the tolerance-limited CMRR weakness identified by AE-013; |
| ANALYSIS | `AE-012` | `docs/decisions/DR-038_SCH101_Precision_Architecture_PROPOSED.md` | 35 | - AE-012 headroom regression passes; |
| ANALYSIS | `AE-012` | `docs/decisions/DR-038_SCH101_Precision_Architecture_SELECTED.md` | 9 | Reason: the current generator, schematic builder, AE-010/AE-012 regressions and |
| SCH101_NUMERIC | `3.48` | `docs/decisions/DR-038_SCH101_Precision_Architecture_SELECTED.md` | 10 | precision/noise assurance suite are mutually coupled to the proven 3.48x |
| DR039 | `DR-039` | `docs/decisions/DR-039_Common_Post_EQ_DC_Block_PROPOSED.md` | 1 | # DR-039 — Proposed common post-EQ DC block |
| ANALYSIS | `AE-015` | `docs/decisions/DR-039_Common_Post_EQ_DC_Block_PROPOSED.md` | 5 | **Evidence:** AE-015 |
| DR039 | `1.0 µF` | `docs/decisions/DR-039_Common_Post_EQ_DC_Block_PROPOSED.md` | 13 | - C = 1.0 µF film |
| DR039 | `0.48 Hz` | `docs/decisions/DR-039_Common_Post_EQ_DC_Block_PROPOSED.md` | 15 | - fc ≈ 0.48 Hz |
| DR039 | `DR-039` | `docs/decisions/DR-039_Common_Post_EQ_DC_Block_SELECTED.md` | 1 | # DR-039 — Common post-EQ DC block |
| DR039 | `1.0 µF` | `docs/decisions/DR-039_Common_Post_EQ_DC_Block_SELECTED.md` | 7 | - 1.0 µF non-polar film series capacitor per channel; |
| DR039 | `0.48 Hz` | `docs/decisions/DR-039_Common_Post_EQ_DC_Block_SELECTED.md` | 10 | - nominal corner approximately 0.48 Hz. |
| DR039 | `DR-039` | `docs/decisions/DR-039_Common_Post_EQ_DC_Block_SELECTED.md` | 12 | DR-039 is not yet substituted into the active SCH103 generator. It shall be |
| ANALYSIS | `AE-012` | `docs/updates/AE012_UPDATE_MANIFEST.md` | 1 | # AE-012 update manifest |
| ANALYSIS | `signal_chain_analysis` | `docs/updates/AE012_UPDATE_MANIFEST.md` | 6 | - `generator/model/signal_chain_analysis.py` |
| ANALYSIS | `signal_chain_analysis` | `docs/updates/AE012_UPDATE_MANIFEST.md` | 7 | - `tests/test_signal_chain_analysis.py` |
| ANALYSIS | `AE-012` | `docs/updates/AE012_UPDATE_MANIFEST.md` | 10 | - `docs/AE-012_All_State_Gain_Headroom_Closure_Rev_A0.md` |
| ANALYSIS | `AE-013` | `docs/updates/AE013_UPDATE_MANIFEST.md` | 1 | # AE-013 update manifest |
| ANALYSIS | `sch101_precision_analysis` | `docs/updates/AE013_UPDATE_MANIFEST.md` | 6 | - `generator/model/sch101_precision_analysis.py` |
| ANALYSIS | `sch101_precision_analysis` | `docs/updates/AE013_UPDATE_MANIFEST.md` | 7 | - `tests/test_sch101_precision_analysis.py` |
| ANALYSIS | `AE-013` | `docs/updates/AE013_UPDATE_MANIFEST.md` | 8 | - `docs/AE-013_SCH101_Noise_CMRR_Review_Rev_A0.md` |
| ANALYSIS | `AE-014` | `docs/updates/AE014_UPDATE_MANIFEST.md` | 1 | # AE-014 update manifest |
| ANALYSIS | `sch101_precision_candidate` | `docs/updates/AE014_UPDATE_MANIFEST.md` | 6 | - generator/model/sch101_precision_candidate.py |
| ANALYSIS | `sch101_precision_candidate` | `docs/updates/AE014_UPDATE_MANIFEST.md` | 7 | - tests/test_sch101_precision_candidate.py |
| ANALYSIS | `AE-014` | `docs/updates/AE014_UPDATE_MANIFEST.md` | 8 | - docs/AE-014_SCH101_Precision_Architecture_Downselect_Rev_A0.md |
| ANALYSIS | `AE-015` | `docs/updates/AE015_UPDATE_MANIFEST.md` | 1 | # AE-015 update manifest |
| ANALYSIS | `signal_chain_noise_dc` | `docs/updates/AE015_UPDATE_MANIFEST.md` | 6 | - `generator/model/signal_chain_noise_dc.py` |
| ANALYSIS | `signal_chain_noise_dc` | `docs/updates/AE015_UPDATE_MANIFEST.md` | 7 | - `tests/test_signal_chain_noise_dc.py` |
| ANALYSIS | `AE-015` | `docs/updates/AE015_UPDATE_MANIFEST.md` | 8 | - `docs/AE-015_Full_Chain_Noise_DC_Review_Rev_A0.md` |
| DR039 | `DR-039` | `docs/updates/AE015_UPDATE_MANIFEST.md` | 9 | - `docs/decisions/DR-039_Common_Post_EQ_DC_Block_PROPOSED.md` |
| DR039 | `post_eq_dc_block` | `docs/updates/AE016A_UPDATE_MANIFEST.md` | 13 | - generator/model/post_eq_dc_block.py |
| DR039 | `DR-039` | `docs/updates/AE016A_UPDATE_MANIFEST.md` | 14 | - DR-039 SCH103 physical patch |
| ANALYSIS | `signal_chain_analysis` | `docs/updates/AE016A_UPDATE_MANIFEST.md` | 17 | - AE-016 `signal_chain_analysis.py` modification. |
| ANALYSIS | `signal_chain_analysis` | `docs/updates/AE016A_UPDATE_MANIFEST.md` | 19 | If AE-016 already modified `signal_chain_analysis.py`, run the repair script |
| SCH103_OUTPUT | `replay_eq.py` | `docs/updates/AE016B_UPDATE_MANIFEST.md` | 6 | - restore `generator/blocks/replay_eq.py` to its pre-DR039 physical baseline; |
| DR039 | `post_eq_dc_block` | `docs/updates/AE016B_UPDATE_MANIFEST.md` | 7 | - retain `generator/model/post_eq_dc_block.py`; |
| DR039 | `DR-039` | `docs/updates/AE016B_UPDATE_MANIFEST.md` | 8 | - restage DR-039 as SELECTED / CAD migration pending; |
| ANALYSIS | `AE-012` | `docs/updates/AE016B_UPDATE_MANIFEST.md` | 10 | - restore the AE-012 signal-chain calculation if it is still patched. |
| DR039 | `post_eq_dc_block` | `docs/updates/AE016_UPDATE_MANIFEST.md` | 9 | - generator/model/post_eq_dc_block.py |
| DR039 | `DR-039` | `docs/updates/AE016_UPDATE_MANIFEST.md` | 11 | - selected DR-038 / DR-039 decision records |
| SCH103_OUTPUT | `replay_eq.py` | `docs/updates/AE016_UPDATE_MANIFEST.md` | 15 | - generator/blocks/replay_eq.py |
| ANALYSIS | `signal_chain_analysis` | `docs/updates/AE016_UPDATE_MANIFEST.md` | 16 | - generator/model/signal_chain_analysis.py |
| DR039 | `DR-039` | `docs/updates/AE016_UPDATE_MANIFEST.md` | 24 | `git commit -m "feat(signal-chain): implement DR-038 precision gain and DR-039 DC block"` |
| DR039 | `DR-039` | `docs/updates/AE017_UPDATE_MANIFEST.md` | 22 | `git commit -m "analysis(migration): map DR-038 and DR-039 atomic dependencies"` |
| ANALYSIS | `signal_chain_analysis` | `docs/updates/DR037_UPDATE_MANIFEST.md` | 18 | - `generator/model/signal_chain_analysis.py` |
| ANALYSIS | `signal_chain_analysis` | `docs/updates/DR037_UPDATE_MANIFEST.md` | 24 | - `tests/test_signal_chain_analysis.py` |
| SCH101_NUMERIC | `DIFF_CONVERTER_GAIN` | `generator/blocks/balanced_input.py` | 23 | DIFF_CONVERTER_GAIN, |
| SCH101_NUMERIC | `GAIN_BASE_RF_OHM` | `generator/blocks/balanced_input.py` | 24 | GAIN_BASE_RF_OHM, |
| SCH101_NUMERIC | `GAIN_DEFAULT_ADD_OHM` | `generator/blocks/balanced_input.py` | 25 | GAIN_DEFAULT_ADD_OHM, |
| SCH101_NUMERIC | `GAIN_HIGH_ADD_OHM` | `generator/blocks/balanced_input.py` | 26 | GAIN_HIGH_ADD_OHM, |
| SCH101_NUMERIC | `GAIN_RG_OHM` | `generator/blocks/balanced_input.py` | 27 | GAIN_RG_OHM, |
| SCH101_CAD | `DIP_Switch_Block` | `generator/blocks/balanced_input.py` | 50 | lib_id="ProjectShellac:DIP_Switch_Block", |
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
