CGShepherd/Shellac/docs/procurement/Shellac_Running_BOM_Cost.md

# Shellac Running BOM Cost

**Price snapshot:** 2026-09-03

## Dashboard

- Verified/estimated design-BOM subtotal: **£233.67 ex VAT**
- Verified/estimated one-build subtotal: **£233.67 ex VAT**
- Known 10-unit-price subtotal: **£40.32 ex VAT**
- Priced ledger lines: **4/5**
- Cost coverage: **80.0%**
- Unpriced ledger lines: **1**

> These are partial subtotals until every product-BOM category is priced.

## Category subtotal — design basis

- controls: **£23.82**
- enclosure_mechanics: **£187.10**
- psu: **£22.75**

## Product cost ledger

| ID | Category | Description | Status | Design | One-build | 10-unit ref | Confidence | Source/date |
|---|---|---|---|---:|---:|---:|---|---|
| COST-CTRL-ROTARY | controls | Lorlin PT production rotary set | UNQUOTED | UNQUOTED | UNQUOTED | UNQUOTED | OPEN | — |
| COST-CTRL-TOGGLES | controls | 2 x C&K 7201SYCBE | VERIFIED_SNAPSHOT | £23.82 | £23.82 | £20.56 | HIGH | DigiKey UK / 2026-09-03 |
| COST-ENC-AUDIO | enclosure_mechanics | METCASE M5502119 audio enclosure | VERIFIED_SNAPSHOT | £93.55 | £93.55 | UNQUOTED | HIGH | RS UK / 2026-09-03 |
| COST-ENC-PSU | enclosure_mechanics | METCASE M5502119 PSU enclosure | VERIFIED_SNAPSHOT | £93.55 | £93.55 | UNQUOTED | HIGH | RS UK / 2026-09-03 |
| COST-PSU-MAINS | psu | SCHURTER KMF1.1121.11 filtered mains entry | VERIFIED_SNAPSHOT | £22.75 | £22.75 | £19.76 | HIGH | Farnell UK / 2026-09-03 |

## NRE / prototype-only costs

- NRE-PT-SAMPLES: £28.00 ex VAT — Lorlin PT mechanical validation samples
