CGShepherd/Shellac/mechanical/mcad/reports/AE076B2B_KiCad_STEP_Export_Evidence.txt

AE-076B2B KiCad STEP Export Evidence
source commit: 1e8702139db68ef42bd0c2dd414db99524948309
source board SHA-256: 2e8934d9357f85cda82a47e7a19524c5fd76b1d8357f6c2a95cfaa559b0b1417
KiCad version: 9.0.7
output bytes: 1711778
output SHA-256: 9e391adf01377ebdb3b58b5cd36bee400b8df176be434acb723e95324fad2646

Exporter output:
Determining PCB data.
Build STEP data.
Adding component R103.
Adding component R7002.
Adding component U700.
Adding component C35020.
Adding component C75094.
Adding component R222.
Adding component R35012.
Adding component C90042.
Adding component R30013.
Adding component C90043.
Adding component C35051.
Adding component C30015.
Adding component R7701.
Adding component R75090.
Adding component R7501.
Adding component C80040.
Adding component C191.
Adding component C80043.
Adding component R909.
Adding component R214.
Adding component C30011.
Adding component C75093.
Adding component H120.
Adding component C193.
Adding component C90020.
Adding component C293.
Adding component C35024.
Adding component U3501.
Adding component C292.
Adding component C35021.
Adding component C7202.
Adding component R223.
Adding component D90033.
Adding component R224.
Adding component R904.
Adding component R105.
Adding component R4002.
Adding component R906.
Adding component FB8002.
Adding component R35060.
Adding component H111.
Adding component C75091.
Adding component C5091.
Adding component R123.
Adding component C70094.
Adding component U9001.
Adding component C102.
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
Build board outlines (1 outlines) with 4 points.
Build board cutouts and holes (160 hole(s)).
Subtracting holes for shapes
Subtracting holes for pads
Subtracting holes for vias
Generate board full shape.
Writing STEP file.
*******************************************************************
******        Statistics on Transfer (Write)                 ******
*******************************************************************
******        Transfer Mode = 0  I.E.  As Is       ******
******        Transferring Shape, ShapeType = 0                      ******
** WorkSession : Sending all data
 Step File Name : $tempfile$.step(35959 ents)  Write  Done
STEP file 'C:\Users\chris\Dropbox\000_Projects\000_Audio\Shellac\mechanical\mcad\pcb\generated\ProjectShellac_AE076B2A.step' created.
Export time 1.301 s

FIX2 missing 3D model refs: C30060,C35060,H901
FIX2 geometry complete: False
