CGShepherd/Shellac/simulation/results/ae076a_17v/ae076a_output_pre90_17v.md

# AE-076A +/-17 V output and PRE90 requalification

Status: **PASS_17V_OUTPUT_PRE90_REQUALIFICATION_BENCH_GATES_RETAINED**

- Worst absolute 2 kOhm insertion loss vs 100 kOhm: 0.209239 dB
- Minimum 3.21 Vrms / 10 kOhm margin to 10 Vrms design ceiling: 3.9128 dB
- Maximum high-gain PRE90 output at 4.66 Vrms THAT1646 input: 9.071872 Vrms
- Maximum high-gain compression fraction: 0.00000000
- Minimum margin to PRE90 9.3 Vrms @ 0 dB sensitivity: 0.2157 dB

Historical AE-069 and AE-075G evidence is unchanged.
RUN06 load/cable stability and dynamic-THD bench gates remain open.
RUN08 overload/recovery, RUN13 rail variation and RUN14 phantom-fault work remain open.
Powered PSU setpoint/dropout/ripple/startup/thermal qualification remains open.
