CGShepherd/Shellac/simulation/results/ae075g_pre90_output/ae075g_pre90_output.md

# AE-075G PRE90 2 kOhm discriminator

Status: **LOAD_COMPATIBILITY_PASS_HIGH_LEVEL_MARGIN_REQUIRES_BENCH_CONFIRMATION**

- Worst absolute insertion loss vs 100 kOhm: 0.209239 dB
- Worst passband peak: 0.000409 dB
- Load discriminator: PASS

## Loaded representative Shellac outputs
- nominal_5mV_default: 0.626735 Vrms; margin to 9.3 Vrms @0 dB = 23.4280 dB
- worst_default: 5.720666 Vrms; margin to 9.3 Vrms @0 dB = 4.2207 dB
- worst_high_gain: 9.098397 Vrms; margin to 9.3 Vrms @0 dB = 0.1904 dB

Historical AE-069 RUN06 evidence is unchanged.
RUN06 load/cable stability and dynamic-THD bench gates remain open.
H801/H802 XY remains provisional pending manual placement reconciliation.
