CGShepherd/Shellac/simulation/results/run07_end_to_end/ae070_run07.md

# AE-070 RUN07 summary

Status: **QUALIFIED_NOMINAL_REPRESENTATIVE_STATES**

Representative cases: 5; ferrite-bracket executions: 10.
Replay/track gates: PASS.
Rumble integrated gate: PASS.
Mono integrated insertion gate: PASS.

RUN08 headroom/overload, RUN09 noise, RUN10 sensitivity, RUN12 switching, RUN13 rails and RUN14 phantom remain open.
