CGShepherd/Shellac/simulation/results/run06_output/ae069_run06.md

# AE-069 RUN06 summary

- Worst normal-load gain variation: 0.038809 dB
- Worst normal-load passband peak: 0.000419 dB
- 600 Ohm AC gain droop range: -0.6880 to -0.6873 dB
- 600 Ohm quasi-static harmonic-distortion estimate: 0.000001% to 0.000001%
- Worst 10 kOhm 3.21 Vrms margin to 10 Vrms design ceiling: 3.9128 dB

- Normal-load gain/peaking gate: PASS
- DC-offset absolute gate: PASS
- Exact-topology HF small-signal AC evidence: COMPLETE
- Reproducible transient load-stability qualification: NO — combined vendor-model transient solve is non-reproducible
- Prototype load/cable stability bench gate: REQUIRED
- 10 kOhm severe-input headroom minimum: PASS
- 600 Ohm distortion estimate recorded: PASS

Controlled THAT1646 periodic large-signal transient convergence limitation is confirmed in the minimal device circuit.
The distortion figure above is a quasi-static nonlinear-transfer harmonic estimate, NOT transient 1 kHz THD.
Audio-band/quasi-static ferrite calculations use R-L engineering brackets; high-frequency small-signal stability uses controlled official Murata models.
RUN08/RUN09/RUN10/RUN13/RUN14 plus transient-THD and bench correlation remain open.
