CGShepherd/Shellac/simulation/results/run05_matrix/ae068_run05.md

# AE-068 RUN05 summary

- Direct-path worst insertion: 0.000861 dB — PASS
- Mono equal insertion L/R @1k: -0.018608 / -0.018608 dB — PASS
- Mono nominal weight mismatch @1k: 0.000000%
- Stereo separation @ 5.0 pF bracket: 98.02 dB @1k, 72.00 dB @20k — PASS

Full switching transient remains RUN12; full-system noise remains RUN09; tolerance/sensitivity remains RUN10.
