CGShepherd/Shellac/simulation/results/run04_lf_trade/ae067_run04.md

# AE-067 RUN04 DR039/SCH107 LF trade — Phase A evidence

Status: **EVIDENCE_COMPLETE_REVIEW_REQUIRED**

| Candidate | LF hard | 20 Hz direct | 15 Hz f3 | 20 Hz filter | Filter noise Δ | Switch peak |
|---|---|---:|---:|---:|---:|---:|
| CURRENT_COMMON_PRE_SPLIT | FAIL | -1.5104 dB | 17.363 Hz | -1.9714 dB | +0.099 dB | 3.79 mV |
| POST_SWITCH_COMMON | PASS | -0.0025 dB | 15.049 Hz | -0.4635 dB | +0.000 dB | 249.50 mV |
| BRANCH_LOCAL_DIRECT_BYPASS_BLOCK | PASS | -0.0025 dB | 15.045 Hz | -0.4610 dB | +0.000 dB | 3.79 mV |
| RUMBLE_SCALE10_COMMON_1P2UF | FAIL | -0.1219 dB | 15.203 Hz | -0.5831 dB | +1.658 dB | 3.79 mV |

No topology is auto-promoted by Phase A. Review frequency, noise, DC-step settling, selector charge transient and value-engineering together before governance changes.

Full system noise remains RUN09, component sensitivity/tolerance remains RUN10, and SW904-to-XLR switching remains RUN12.
