CGShepherd/Shellac/simulation/results/ae066_summary.md

# AE-066 simulation summary

Campaign status: **PASS_WITH_GRADO_EXTENDED_BAND_OPEN**

- RUN01: PARTIAL_GRADO_EXTENDED_BAND_MODEL_VALIDITY_OPEN (45 cases)
- RUN02: QUALIFIED_NOMINAL (3 gain states)
- RUN03: QUALIFIED_NOMINAL_ALL_25_STATES (25 Bass x Treble states)
- RUN01 loading combinations not meeting both AE-049 peaking limits: 36
- RUN03 worst model/analytical correlation error: 0.001118 dB
- RUN03 worst named target error: 0.031294 dB (500_Hz_78__1600_Hz)
- RIAA target error: 0.008280 dB
- Largest RUN03 representative DC magnitude: 0.015884 V (200_Hz__FLAT)
- Open findings: GRADO_78C_EXTENDED_20_TO_50KHZ_MODEL_VALIDITY, RUN01_LOADING_MATRIX_CONTAINS_REJECTED_OR_REVIEW_COMBINATIONS

This summary is evidence for selected-next candidate analysis only. It does not migrate the product generator.
