CGShepherd/Shellac/simulation/config/integrated_baseline.yaml

schema_version: 1
authority:
  qualification: AE-048
  acceptance: AE-049
  execution: AE-050
  toolchain: AE-053
  configuration_semantics: AE-059
  integrated_contract: AE-060
  model_source_closure: AE-064
  rail_reconciliation: AE-076A

top_level: SHELLAC_TOP
nominal_rails_v:
  plus: 17.0
  minus: -17.0

rail_authority_requalification:
  authority: AE-076A
  status: PASSED_17V_REQUALIFICATION
  historical_18v_evidence_preserved: true
  baseline_commit: d2f5c9f775b6080c66a9754a8355c7692cd4ba6a
  integrated_run00_result: simulation/results/ae076a_17v/ae076a_integrated_run00_17v.json
  output_pre90_result: simulation/results/ae076a_17v/ae076a_output_pre90_17v.json
  powered_psu_setpoint_dropout_ripple_startup_thermal: OPEN_RUN13_RUN14_BENCH
  routing_authority_changed: false

model_semantics:
  product_generator: LIVE_IMPLEMENTATION
  integrated_spice: SELECTED_NEXT_CANDIDATE_ANALYSIS
  generator_migration_implied: false

required_hierarchy:
  - SRC_CARTRIDGE_L
  - SRC_CARTRIDGE_R
  - SCH101_L
  - SCH101_R
  - SCH103_L
  - SCH103_R
  - DR039_SCH107_L
  - DR039_SCH107_R
  - SCH104_L
  - SCH104_R
  - SCH105_MATRIX
  - SCH105_BUF_L
  - SCH105_BUF_R
  - SW905_MUTE
  - SCH108_L
  - SCH108_R
  - LOAD_BALANCED_L
  - LOAD_BALANCED_R
  - PSU_PLUS18
  - PSU_MINUS18
  - CHASSIS_GROUND_MODEL

canonical_nodes:
  - VIN_CART_L
  - VIN_CART_R
  - N101_L_OUT
  - N101_R_OUT
  - N103_L_LF
  - N103_R_LF
  - N103_L_OUT
  - N103_R_OUT
  - N107_L_IN
  - N107_R_IN
  - N107_L_OUT
  - N107_R_OUT
  - N107_L_BYPASS
  - N107_R_BYPASS
  - N104_L_OUT
  - N104_R_OUT
  - MONO_AVG
  - MONO_R_LEG
  - N105_L_IN
  - N105_R_IN
  - N105_L_OUT
  - N105_R_OUT
  - N108_L_IN
  - N108_R_IN
  - XLR_L_POS
  - XLR_L_NEG
  - XLR_R_POS
  - XLR_R_NEG
  - VPLUS17
  - VMINUS17
  - ZERO_VA
  - CHASSIS

required_parameters:
  - CARTRIDGE
  - GAIN
  - BASS
  - TREBLE
  - RUMBLE
  - MODE
  - MUTE
  - CABLE_PF
  - LOAD_CAP_STATE
  - OUTPUT_LOAD
  - OUTPUT_CABLE_PF
  - LF_TOPOLOGY
  - RAIL_PLUS
  - RAIL_MINUS
  - RAIL_RIPPLE
  - BBM_TIME
  - SWITCH_PARASITIC_PF
  - TEMP
  - TOLERANCE_MODE
  - MC_SEED

selected_next_contract:
  sch101:
    authority: AE-042
    product_migration_authority: AE-071A
    product_generator_status: CURRENT_ARCHITECTURE_QUALIFICATION_OPEN
    product_generator_migrated: true
    candidate_analysis_remains_qualification_evidence: true
    gain_db: [14, 18, 22]
    no_shunt_state_db: 18
    converter_gain: 4.0
    service_cap_pf: [0, 47, 100]
    follow_on_qualification: [RUN10, BENCH]
  dr039_sch107:
    authority: AE-067
    product_migration_authority: AE-074
    product_generator_status: CURRENT_ARCHITECTURE_QUALIFICATION_OPEN
    product_generator_migrated: true
    candidate_analysis_remains_qualification_evidence: true
    preferred_candidate: BRANCH_LOCAL_DIRECT_BYPASS_BLOCK
    selected_topology: BRANCH_LOCAL_DIRECT_BYPASS_BLOCK
    direct_branch_c_f: 1.0e-6
    direct_branch_r_ohm: 330000
    filtered_branch_dc_blocking: INTRINSIC_SCH107_HIGHPASS
    native_pcb_f8_reconciliation: RECONCILED_BY_AE074
    follow_on_qualification: [RUN09, RUN10, RUN12, BENCH]
  mute:
    authority: AE-059
    type: MECHANICAL_DPDT_INPUT_MUTE
    run_source: CHANNEL_MODE_SIGNAL
    mute_source: ZERO_VA
    automatic_sequencing: false

required_model_sources:
  - {id: LT5400, status: RESOLVED}
  - {id: OPA1612, status: RESOLVED}
  - {id: OPA1656, status: RESOLVED}
  - {id: THAT1646, status: RESOLVED}
  - {id: DIODE_S1G, status: RESOLVED}
  - {id: CARTRIDGE_GRADO_78C, status: RESOLVED}
  - {id: CARTRIDGE_AT_VM95SP, status: RESOLVED}

integrated_run00:
  status: PASSED_NOMINAL_SANITY
  authority: AE-065
  existing_divider_run00_is_toolchain_only: true
  shellac_top_implemented: true
  shellac_top_run00_executed: true
  result_record: simulation/results/run00_sanity/ae065_integrated_run00.json

integrated_ac_campaign:
  authority: AE-066
  status: PASS_WITH_GRADO_EXTENDED_BAND_OPEN
  run01_status: PARTIAL_GRADO_EXTENDED_BAND_MODEL_VALIDITY_OPEN
  run02_status: QUALIFIED_NOMINAL
  run03_status: QUALIFIED_NOMINAL_ALL_25_STATES
  generator_migration_implied: false
  result_summary: simulation/results/ae066_summary.json
  remaining_runs: [RUN08, RUN09, RUN10, RUN11, RUN12, RUN13, RUN14]

run04_lf_trade:
  authority: AE-067
  status: SELECTED_BRANCH_LOCAL_QUALIFICATION_OPEN
  selected_topology: BRANCH_LOCAL_DIRECT_BYPASS_BLOCK
  rejected_topologies:
    - CURRENT_COMMON_PRE_SPLIT
    - POST_SWITCH_COMMON
    - RUMBLE_SCALE10_COMMON_1P2UF
  generator_migration_implied: false
  result_record: simulation/results/run04_lf_trade/ae067_run04.json
  direct_branch_c_f: 1.0e-6
  direct_branch_r_ohm: 330000
  follow_on_qualification: [RUN09, RUN10, RUN12, BENCH]

run05_matrix:
  authority: AE-068
  status: QUALIFIED_STEADY_STATE_TRANSIENT_OPEN
  architecture: AE041_A1_3P4T_PASSIVE_MATRIX
  result_record: simulation/results/run05_matrix/ae068_run05.json
  input_return_ohm: 2200000
  mono_resistor_ohm: 4700
  mono_resistor_current_tolerance_percent: 0.1
  derived_pair_match_percent_preferred_for_run10: 0.10
  derived_pair_match_percent_max_for_run10: 0.25
  tolerance_relaxation_authorised: false
  switch_parasitic_qualification_pf: 5.0
  generator_migration_implied: false
  follow_on_qualification: [RUN09, RUN10, RUN12, BENCH]

run06_output:
  authority: AE-069
  status: SIMULATION_EVIDENCE_COMPLETE_BENCH_GATES_OPEN
  result_record: simulation/results/run06_output/ae069_run06.json
  normal_loads_ohm: [100000, 20000, 10000]
  stress_load_ohm: 600
  worst_normal_gain_variation_db: 0.03880949524
  worst_normal_passband_peak_db: 0.00041935904
  severe_10k_margin_min_db: 3.91280224685
  exact_topology_hf_ac_evidence_complete: true
  transient_stability_reproducibly_qualified: false
  bench_load_stability_required: true
  dynamic_large_signal_thd_qualified: false
  bench_dynamic_thd_required: true
  ferrite_selected: false
  sense_capacitor_mechanical_freeze: false
  generator_migration_implied: false
  follow_on_qualification: [BENCH_LOAD_STABILITY, BENCH_DYNAMIC_THD, FERRITE_SELECTION, SENSE_CAP_MECHANICAL]

run07_end_to_end:
  authority: AE-070
  status: QUALIFIED_NOMINAL_REPRESENTATIVE_STATES
  result_record: simulation/results/run07_end_to_end/ae070_run07.json
  phase_correlation_record: simulation/results/run07_end_to_end/ae070_output_phase_correlation.json
  model_composition_discriminator_record: simulation/results/run07_end_to_end/ae070_model_composition_discriminator.json
  model_composition_limit_confirmed: true
  surrogate_correlation_pass: true
  output_phase_correlation_pass: true
  replay_and_nominal_symmetry_pass: true
  nominal_lr_tracking_semantics: NOMINAL_MODEL_SYMMETRY_ONLY
  tolerance_tracking_deferred_to: [RUN10, RUN11]
  rumble_pass: true
  mono_pass: true
  overload_qualified: false
  noise_qualified: false
  ferrite_selected: false
  bench_correlation_required: true
  generator_migration_implied: false
  follow_on_qualification: [RUN08, RUN09, RUN10, RUN11, RUN12, RUN13, RUN14, BENCH_CORRELATION]
