CGShepherd/Shellac/simulation/config/model_sources.yaml

schema_version: 1
authority: AE-063
purpose: Controlled upstream provenance and ingestion state for integrated Shellac SPICE models.
policy:
  vendor_originals_silently_rewritten: false
  resolve_requires_sha256: true
  resolve_requires_pin_mapping: true
  resolve_requires_wrapper_or_direct_use_record: true
  resolve_requires_sanity_regression: true

sources:
  OPA1656:
    roles: [SCH101_GAIN, SCH101_DIFF_CONVERTER, SCH104_BUFFER, SCH105_BUFFER]
    manufacturer: Texas Instruments
    source_type: VENDOR_PSPICE
    model_title: OPA1656 PSpice Model
    revision: C
    package_id: SBOMAW6C.ZIP
    source_url: https://www.ti.com/product/OPA1656
    status: QUALIFIED_LOCAL_SOURCE
    sha256: 9847ed60c62e792ee6f1c84899278a3c11ce71a6d21804bdd88f51199f1ba055
    local_path: null
    subckt_name: OPA1656
    pin_mapping_verified: true
    wrapper_path: simulation/models/wrappers/opa1656_shellac.lib
    qualification_record: simulation/config/model_qualification.yaml
    redistribution_reviewed: false

  OPA1612:
    roles: [SCH103_ACTIVE_LF]
    manufacturer: Texas Instruments
    source_type: VENDOR_PSPICE
    model_title: OPA161x PSpice Model
    revision: G
    package_id: SBOM396G.ZIP
    source_url: https://www.ti.com/product/OPA1612
    status: QUALIFIED_LOCAL_SOURCE
    sha256: c86df5d4b2d26ec196c0a6158a61004a6747aec5440fcc2031674ad62a448ef7
    local_path: null
    subckt_name: OPA161x
    pin_mapping_verified: true
    wrapper_path: simulation/models/wrappers/opa1612_shellac.lib
    qualification_record: simulation/config/model_qualification.yaml
    redistribution_reviewed: false

  LT5400:
    roles: [SCH101_PRECISION_RESISTOR_NETWORK]
    manufacturer: Analog Devices
    variant: LT5400-7
    source_type: VENDOR_LTSPICE_LIBRARY
    model_title: LT5400 LTspice model/library entry
    source_url: https://www.analog.com/en/products/lt5400.html
    status: QUALIFIED_LOCAL_LIBRARY_SOURCE
    sha256: 259c543f774e7467ebf522c3345e6b7bfccdf35ce43d2373355d0b2b5d183671
    local_path: null
    model_name: LT5400-7
    pin_mapping_verified: true
    wrapper_path: simulation/models/wrappers/lt5400_7_shellac.lib
    qualification_record: simulation/config/model_qualification.yaml
    redistribution_reviewed: false

  THAT1646:
    roles: [SCH108_BALANCED_OUTPUT]
    manufacturer: THAT Corporation
    source_type: VENDOR_SPICE_PACKAGE
    model_title: THAT Corporation Device Models
    revision: "05"
    source_url: https://thatcorp.com/device-models/
    status: QUALIFIED_LOCAL_SOURCE
    sha256: 9abb4f6762935415db6f485de62687fe98b2ef7ea015ed4a320bd158ff264159
    local_path: null
    subckt_name: THAT1646
    pin_mapping_verified: true
    wrapper_path: simulation/models/wrappers/that1646_shellac.lib
    qualification_record: simulation/config/model_qualification.yaml
    redistribution_reviewed: false

  DIODE_S1G:
    roles: [SCH108_PHANTOM_RAIL_CLAMP]
    manufacturer: Vishay General Semiconductor
    source_type: VENDOR_SPICE_MODEL
    model_title: Vishay S1G SPICE model
    source_url: https://www.vishay.com/docs/89655/s1g.txt
    status: QUALIFIED_LOCAL_REFERENCE_SOURCE
    sha256: ffd79ea06d6ab712987b44e577c8787dbe54d25a90de58e3f6901a1b89642ed4
    local_path: null
    model_name: s1g
    pin_mapping_verified: true
    direct_use: true
    qualification_record: simulation/config/model_qualification.yaml
    redistribution_reviewed: false
    qualification_limit: Reference-model provenance and LTspice execution are controlled. Pulse-energy, reverse-recovery relevance, rail injection, powered/unpowered survival and final procured-part equivalence remain open.

  CARTRIDGE_GRADO_78C:
    roles: [PRIMARY_78RPM_CARTRIDGE]
    manufacturer: Grado Labs
    source_type: BEHAVIOURAL_RL_SOURCE
    identity_authority: PROJECT_HARDWARE_BASELINE
    status: PARAMETERS_IDENTIFIED_BENCH_TOPOLOGY_OPEN
    electrical:
      output_v_rms_at_1khz_5cms: 0.005
      dc_resistance_ohm: 475
      inductance_h: 0.045
      recommended_load_ohm: 47000
    evidence:
      quality: SECONDARY_CORROBORATED
      note: Multiple dealer/archive sources agree on nominal R/L/load/output; manufacturer-primary electrical source not yet captured.
    bench_required: [coil_return_topology, body_isolation, left_right_independence]

  CARTRIDGE_AT_VM95SP:
    roles: [SECONDARY_78RPM_CARTRIDGE]
    manufacturer: Audio-Technica
    source_type: BEHAVIOURAL_RL_SOURCE
    source_url: https://docs.audio-technica.com/all/AT-VM95SP_H_UM_112301455_V2_11L_web_180801%20%281%29.pdf
    status: PARAMETERS_IDENTIFIED_OFFICIAL_SOURCE
    electrical:
      output_v_rms_at_1khz_5cms: 0.0027
      dc_resistance_ohm: 485
      inductance_h_at_1khz: 0.550
      recommended_load_ohm: 47000
      recommended_load_capacitance_pf_min: 100
      recommended_load_capacitance_pf_max: 200
    bench_required: [body_isolation_confirmation]
